funkyfourier/keychron-k8pro-case/batteryholder.jpg

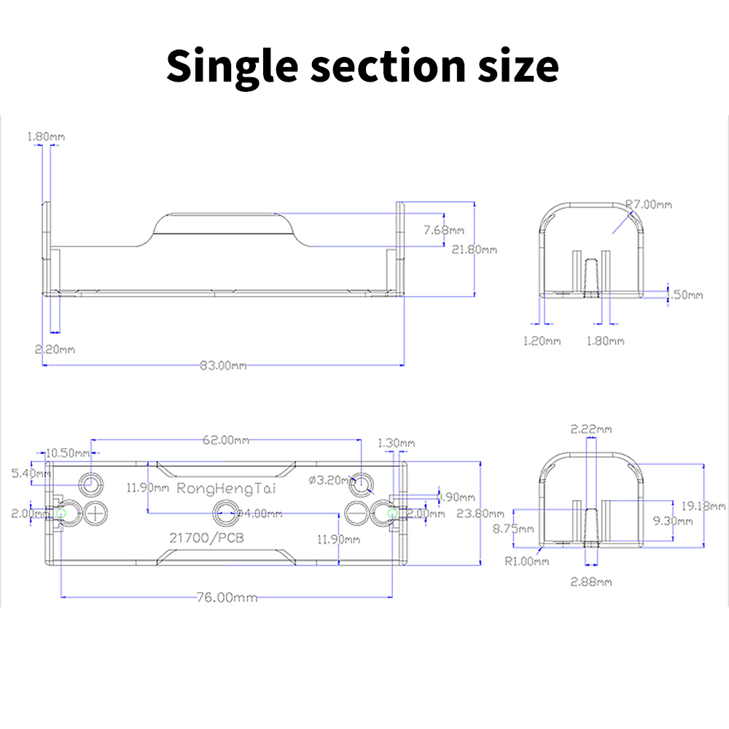
batteryholder.jpg
